mixmesh/pimesh/keyboard/Keyboard/Keyboard.sch

## KiCad design keyboard/Keyboard/Keyboard.sch (2021-03-12, an earlier design)

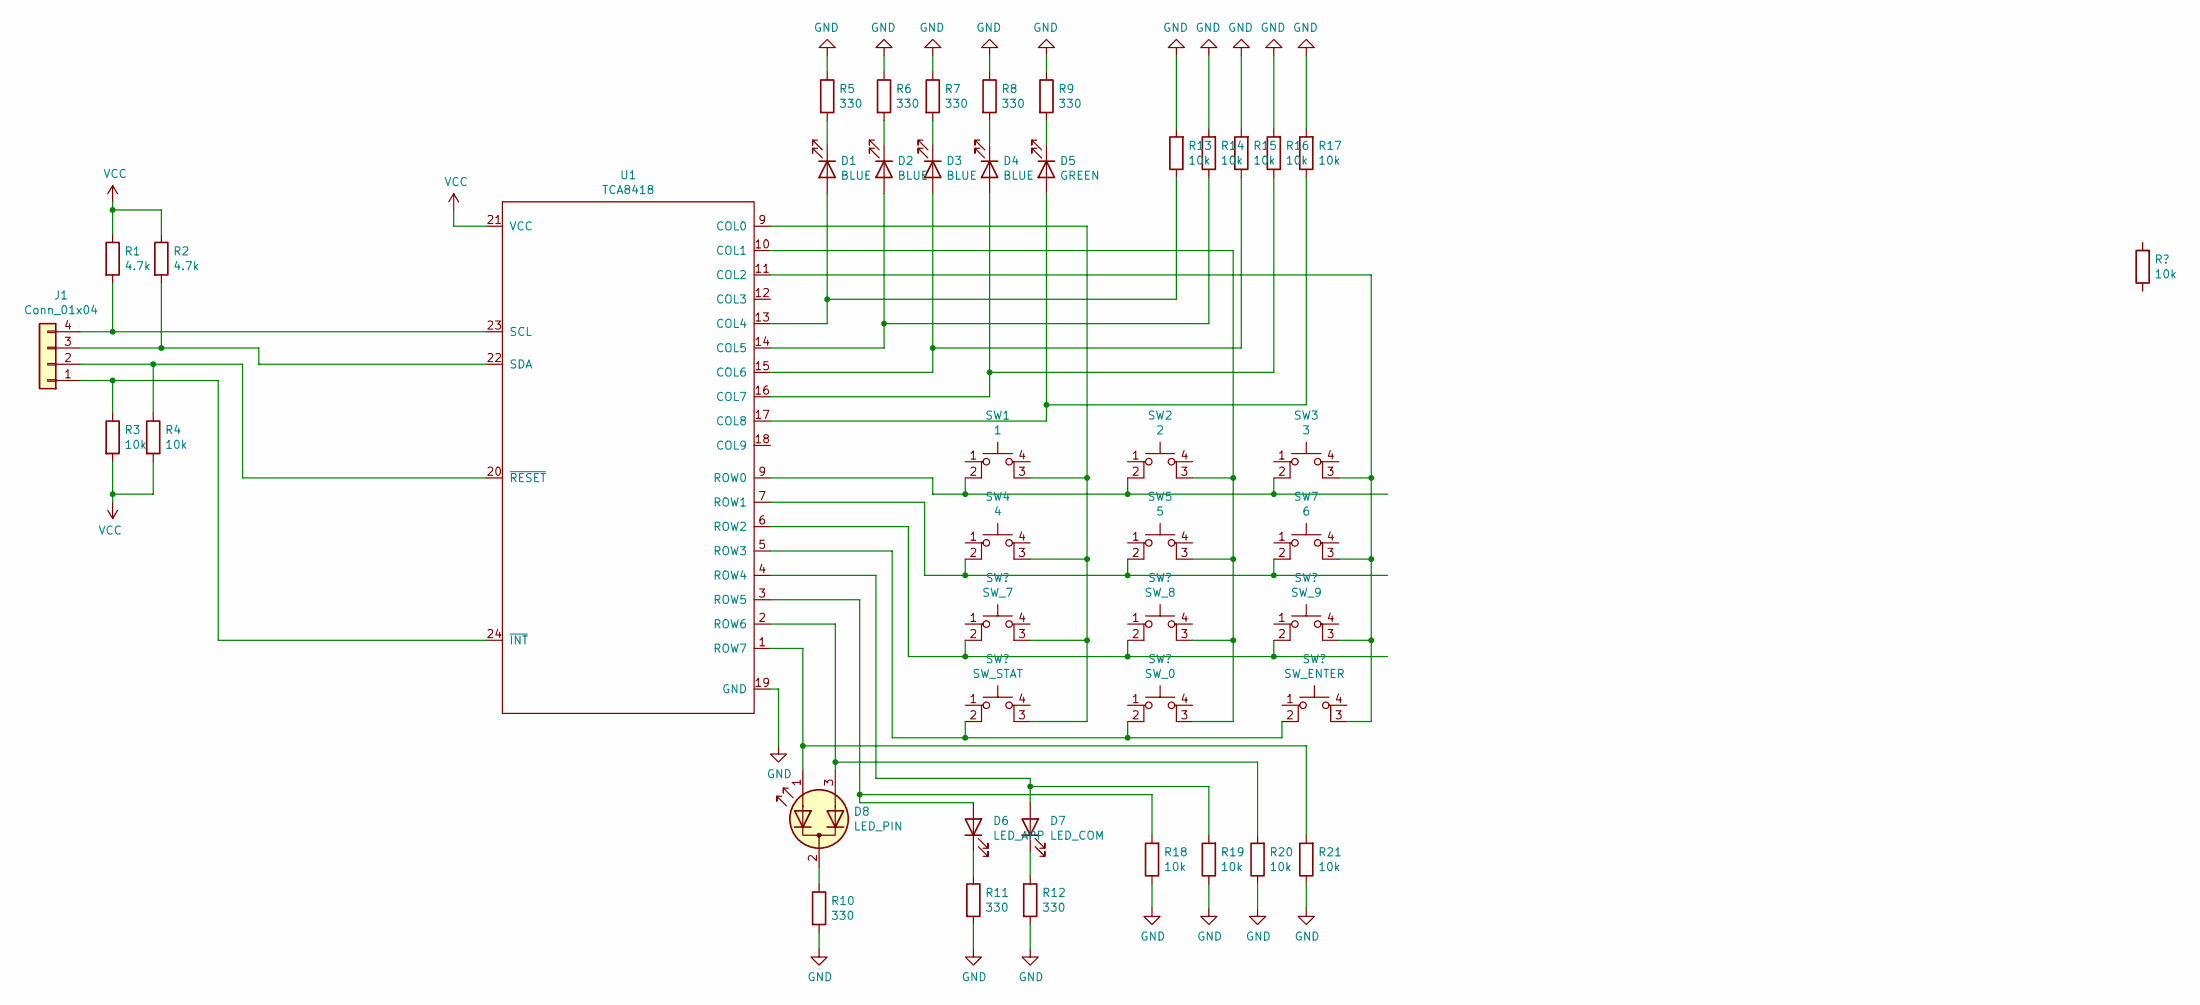
[picture p3: schematic Keyboard.sch]

Parts:
D1, D2, D3, D4: BLUE
D5: GREEN
D6: LED_APP
D7: LED_COM
D8: LED_PIN
J1: Conn_01x04
R1, R2: 4.7k
R3, R4, R13, R14, R15, R16, R17, R18, R19, R20, R21: 10k
R5, R6, R7, R8, R9, R10, R11, R12: 330
SW1: 1
SW2: 2
SW3: 3
SW4: 4
SW5: 5
SW7: 6
U1: TCA8418

Connections:
GND: R5.1, R6.1, R7.1, R8.1, R9.1, R10.2, R11.2, R12.2, R13.2, R14.2, R15.2, R16.2, R17.2, R18.1, R19.1, R20.1, R21.1, U1.19 (GND)
unnamed: D1.1 (K), R5.2
unnamed: D1.2 (A), R13.1, U1.13 (COL4)
unnamed: D2.1 (K), R6.2
unnamed: D2.2 (A), R14.1, U1.14 (COL5)
unnamed: D3.1 (K), R7.2
unnamed: D3.2 (A), R15.1, U1.15 (COL6)
unnamed: D4.1 (K), R8.2
unnamed: D4.2 (A), R16.1, U1.16 (COL7)
unnamed: D5.1 (K), R9.2
unnamed: D5.2 (A), R17.1, U1.17 (COL8)
unnamed: D6.1 (K), R11.1
unnamed: D6.2 (A), R18.2, U1.3 (ROW5)
unnamed: D7.1 (K), R12.1
unnamed: D7.2 (A), R19.2, U1.4 (ROW4)
unnamed: D8.1 (A1), R21.2, U1.1 (ROW7)
unnamed: D8.2 (K), R10.1
unnamed: D8.3 (A2), R20.2, U1.2 (ROW6)
unnamed: J1.1, R3.1, U1.24 (~INT)
unnamed: J1.2, R4.1, U1.20 (~RESET)
unnamed: J1.3, R2.2, U1.22 (SDA)
unnamed: J1.4, R1.2, U1.23 (SCL)
unnamed: SW1.2, SW2.2, SW3.2, U1.9 (COL0)
unnamed: SW1.3 (K), SW4.3 (K), U1.9 (COL0)
unnamed: SW2.3 (K), SW5.3 (K), U1.10 (COL1)
unnamed: SW3.3 (K), SW7.3 (K), U1.11 (COL2)
unnamed: SW4.2, SW5.2, SW7.2, U1.7 (ROW1)
VCC: R1.1, R2.1, R3.2, R4.2, U1.21 (VCC)
